Mottramlabs/MQTT-Power-Sensor/Firmware/Version 2/DRM_MLP191020_Power_PCB/examples/MQTT_Mains_Power_Sensor_MLP191020/MQTT_Settings.h

/*
      MQTT Broker and topic
*/


// MQTT Broker, change as required
const char* mqtt_server = "192.168.1.10";

// MQTT Topics
const char* InStatus = "Mains_Power/Status";
const char* InControl = "Mains_Power/Control";

// the ESP8266's MAC address is normally used to send a message to a selected device. 
// below is the address used to broadcast to all devices subscribed to the above topic.
String Broadcast_All = "*ALL";
